itpcc/IRremote-ATMega8/Result/IR_result.png

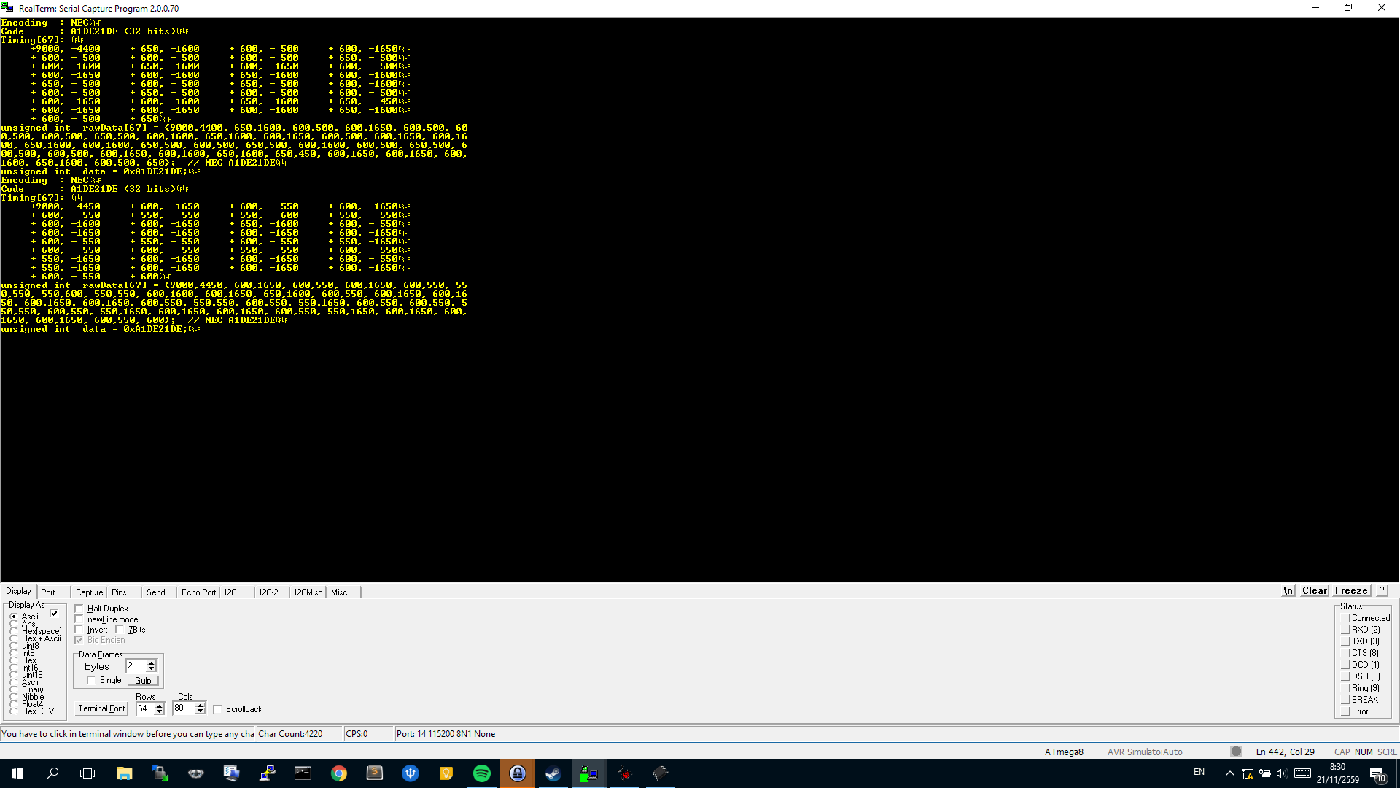
Result/IR_result.png
