itpcc/IRremote-ATMega8/Result/Untitled Sketch_schem.png

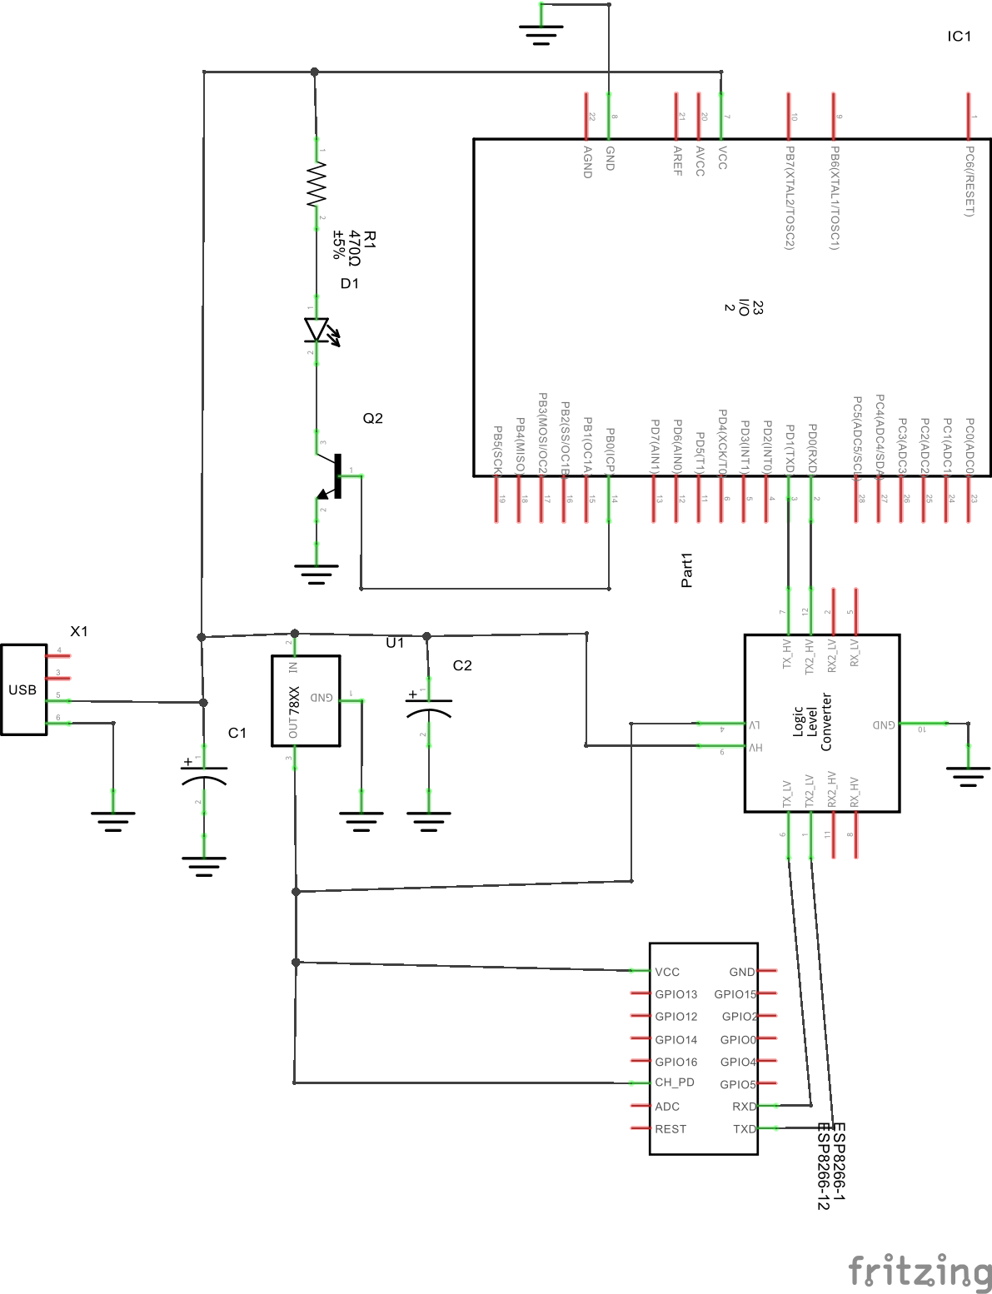
Result/Untitled Sketch_schem.png
