itpcc/IRremote-ATMega8/Schematic/schematic.sch

## EAGLE design Schematic/schematic.sch (2016-12-06)

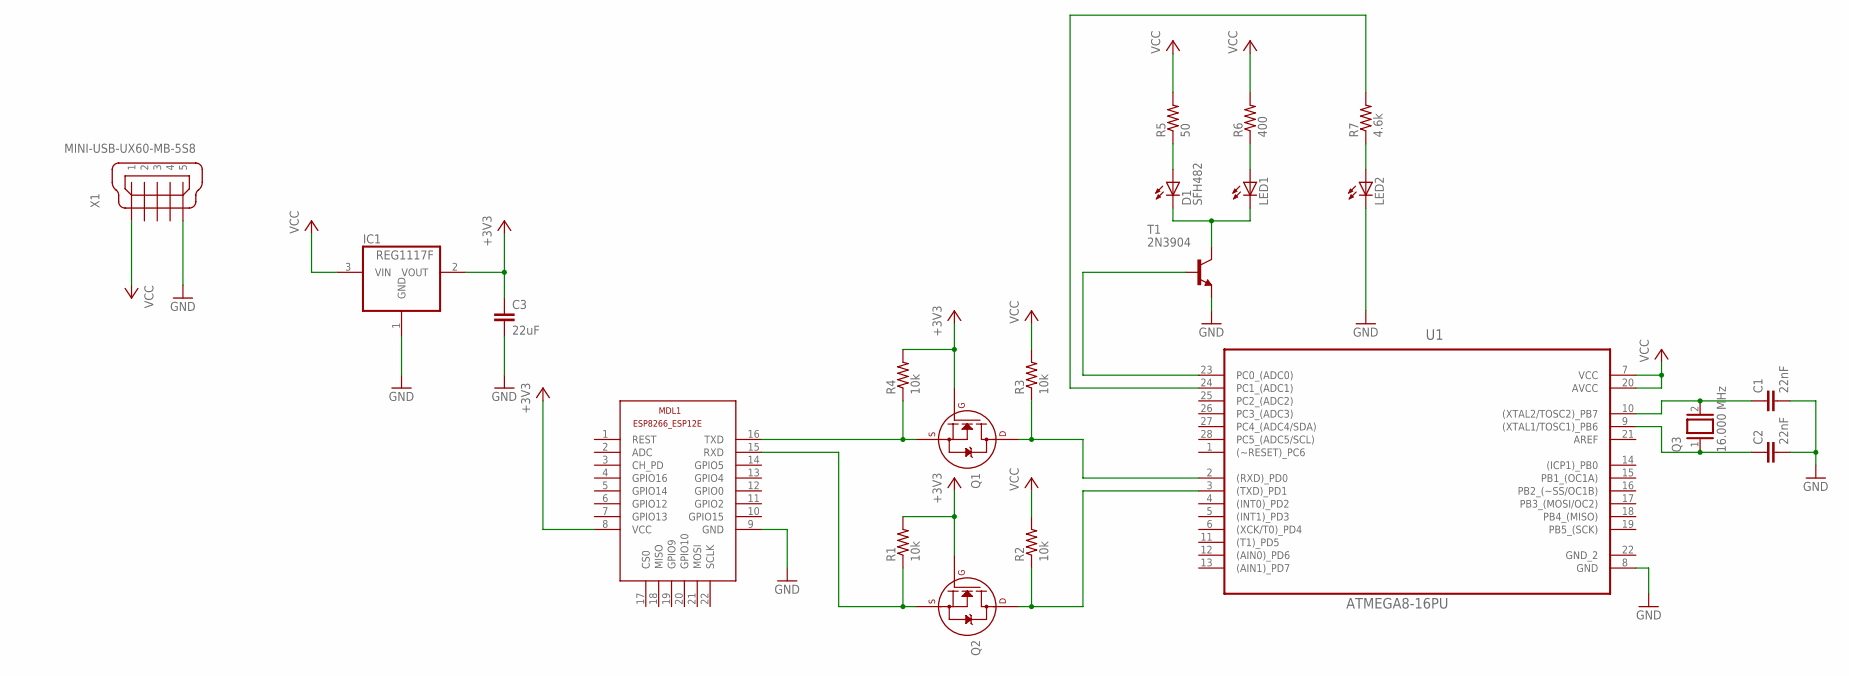
[picture p17: schematic schematic.sch]

Parts:
C1, C2: 22nF; C2.5-3
C3: 22uF; C0805
D1: SFH482
IC1: REG1117F; DD-3
LED1, LED2: LED5MM
MDL1: ESP8266-12EESP8266-ESP12E; ESP8266-ESP12E
Q1, Q2: 2N7000_TO92; TO-92
Q3: 16.000 MHz; Q
R1, R2, R3, R4: 10k; AXIAL-0.3
R5: 50; AXIAL-0.3
R6: 400; AXIAL-0.3
R7: 4.6k; AXIAL-0.3
T1: 2N3904; TO92
U1: ATMEGA8-16PU; DIP254P762X457-28
X1: MINI-USB-UX60-MB-5S8; UX60-MB-5S8

Connections:
+3V3: C3.1, IC1.2 (VOUT), MDL1.8 (VCC), Q1.2 (G), Q2.2 (G), R1.P$2 (2), R4.P$2 (2)
GND: C1.2, C2.2, C3.2, IC1.1 (GND), LED2.K (C), MDL1.9 (GND), T1.3 (E), U1.8 (GND), X1.5
unnamed: MDL1.15 (RXD), Q2.1 (S), R1.P$1 (1)
unnamed: MDL1.16 (TXD), Q1.1 (S), R4.P$1 (1)
unnamed: Q2.3 (D), R2.P$1 (1), U1.3 ((TXD)_PD1)
unnamed: Q1.3 (D), R3.P$1 (1), U1.2 ((RXD)_PD0)
unnamed: T1.2 (B), U1.23 (PC0_(ADC0))
unnamed: D1.A, R5.P$1 (1)
unnamed: LED1.A, R6.P$1 (1)
unnamed: D1.K (C), LED1.K (C), T1.1 (C)
unnamed: LED2.A, R7.P$1 (1)
unnamed: R7.P$2 (2), U1.24 (PC1_(ADC1))
unnamed: C1.1, Q3.2, U1.10 ((XTAL2/TOSC2)_PB7)
unnamed: C2.1, Q3.1, U1.9 ((XTAL1/TOSC1)_PB6)
VCC: IC1.3 (VIN), R2.P$2 (2), R3.P$2 (2), R5.P$2 (2), R6.P$2 (2), U1.7 (VCC), U1.20 (AVCC), X1.1
